PlaymodesStudio/Sonograf/PHOTOS/board_hole.jpg

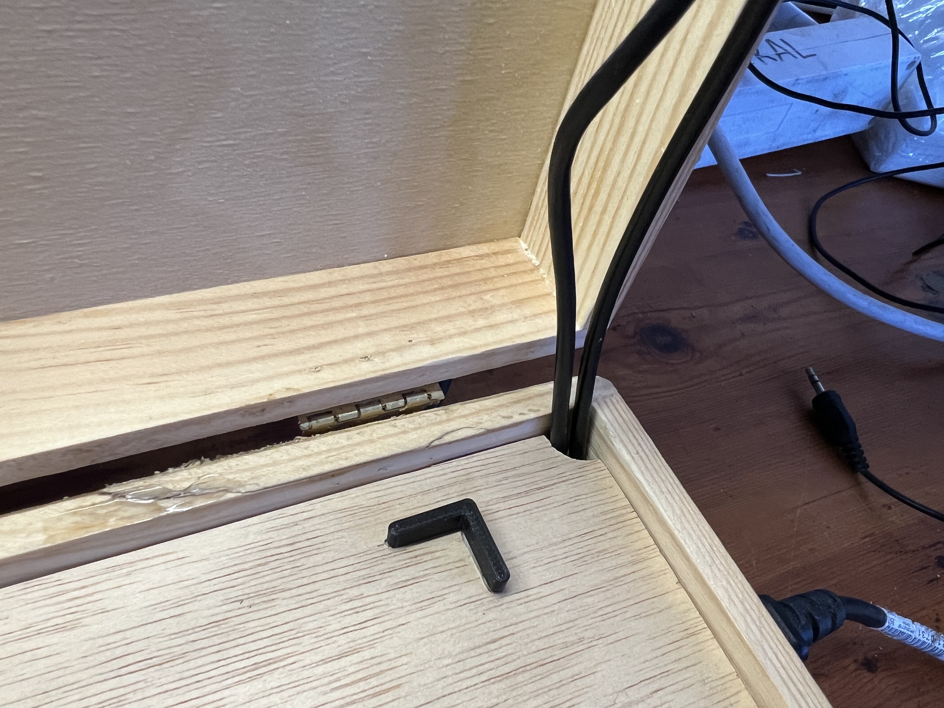
PHOTOS/board_hole.jpg
