PlaymodesStudio/Sonograf/PHOTOS/camera_base.jpg

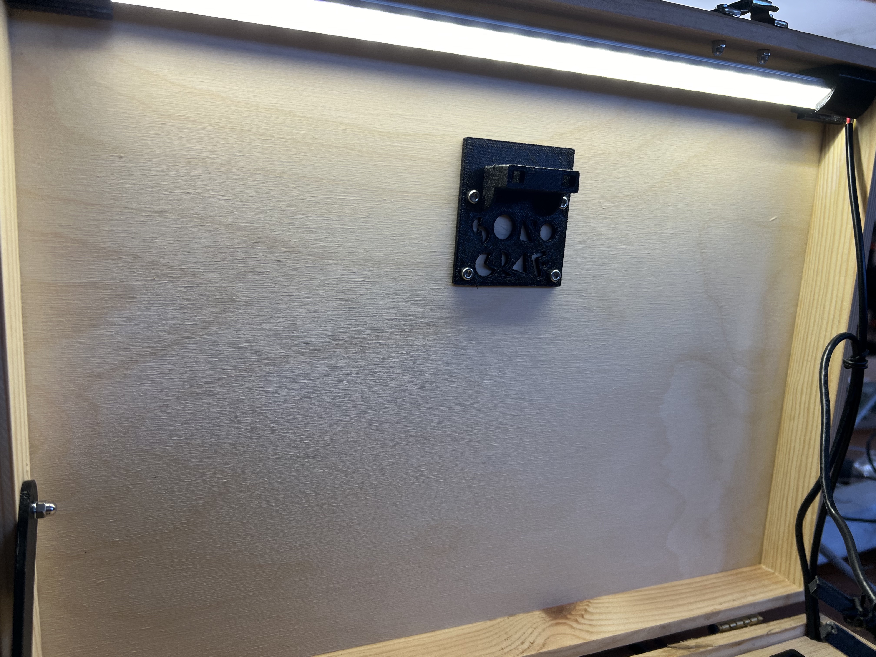
PHOTOS/camera_base.jpg
