PlaymodesStudio/Sonograf/PHOTOS/camera_match.jpg

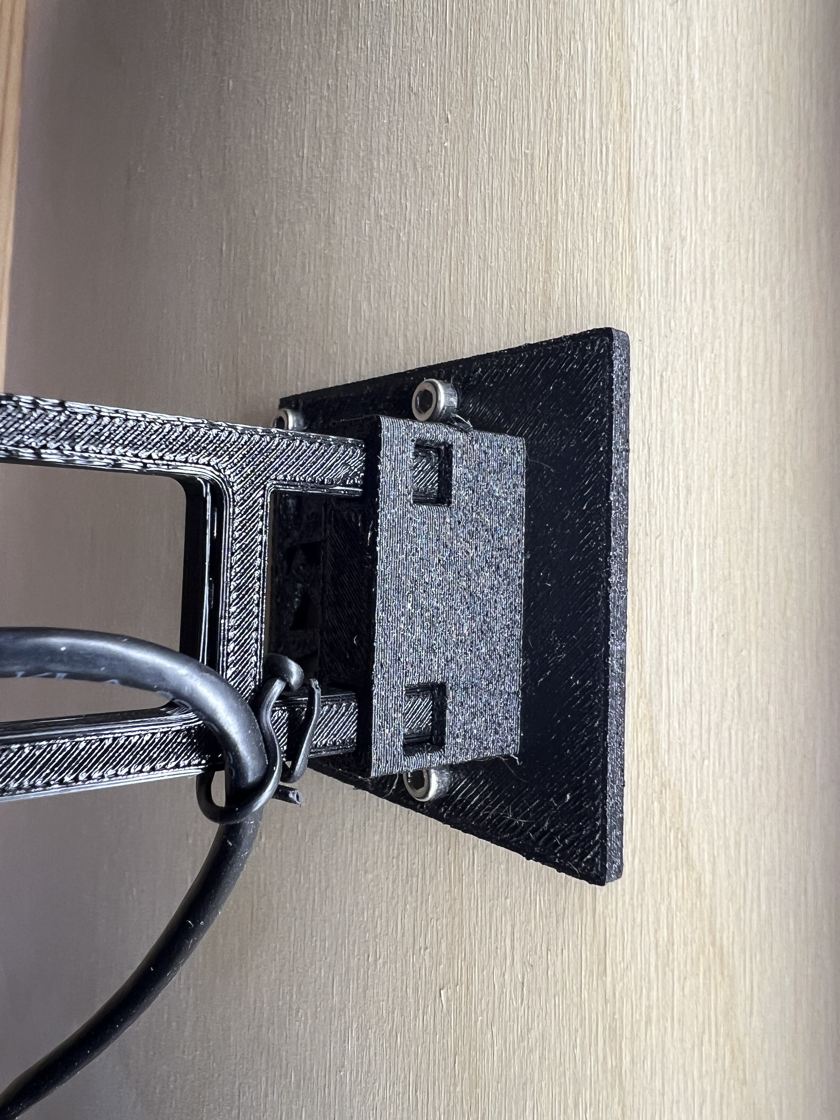
PHOTOS/camera_match.jpg
