PlaymodesStudio/Sonograf/PHOTOS/camera_support.jpg

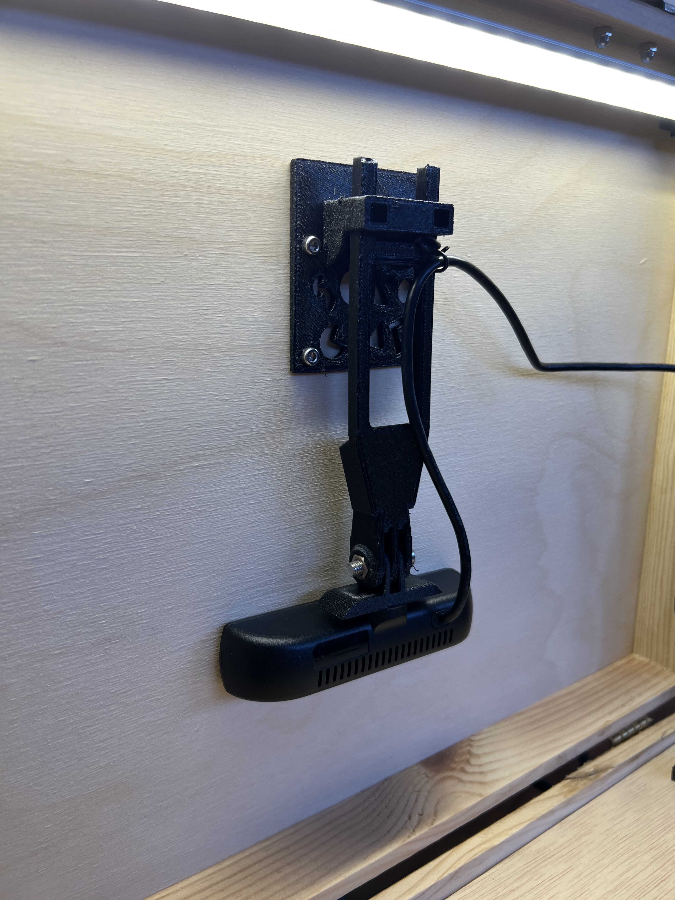
PHOTOS/camera_support.jpg
