PlaymodesStudio/Sonograf/PHOTOS/case_cover.jpg

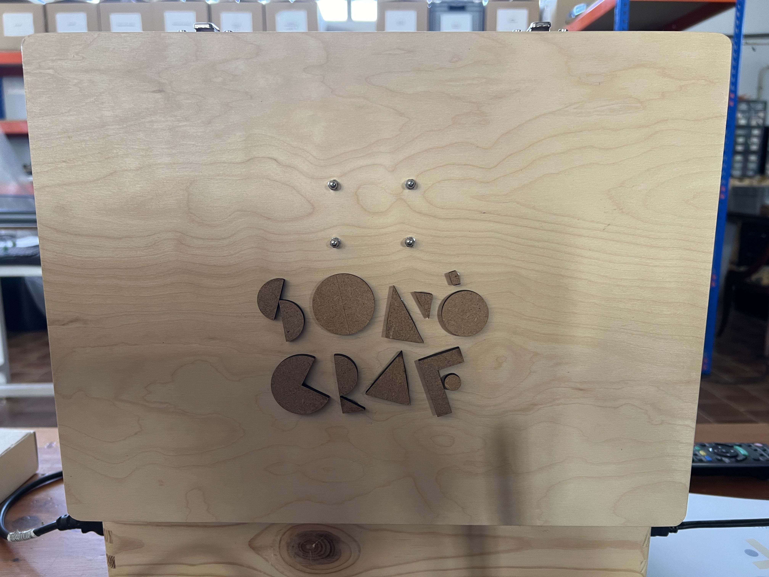
PHOTOS/case_cover.jpg
