PlaymodesStudio/Sonograf/PHOTOS/diagram.png

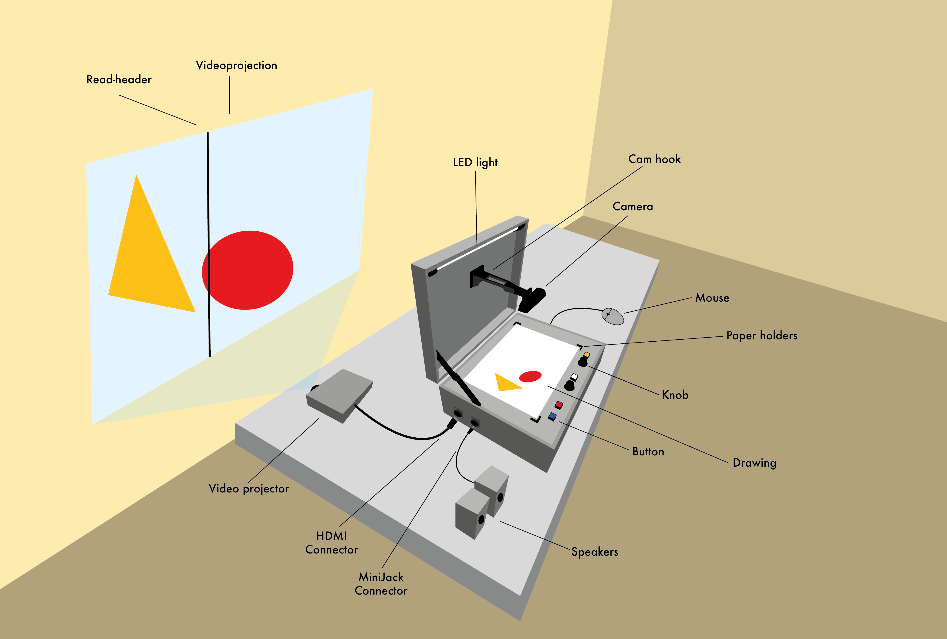
PHOTOS/diagram.png
