PlaymodesStudio/Sonograf/PHOTOS/HDMI.jpg

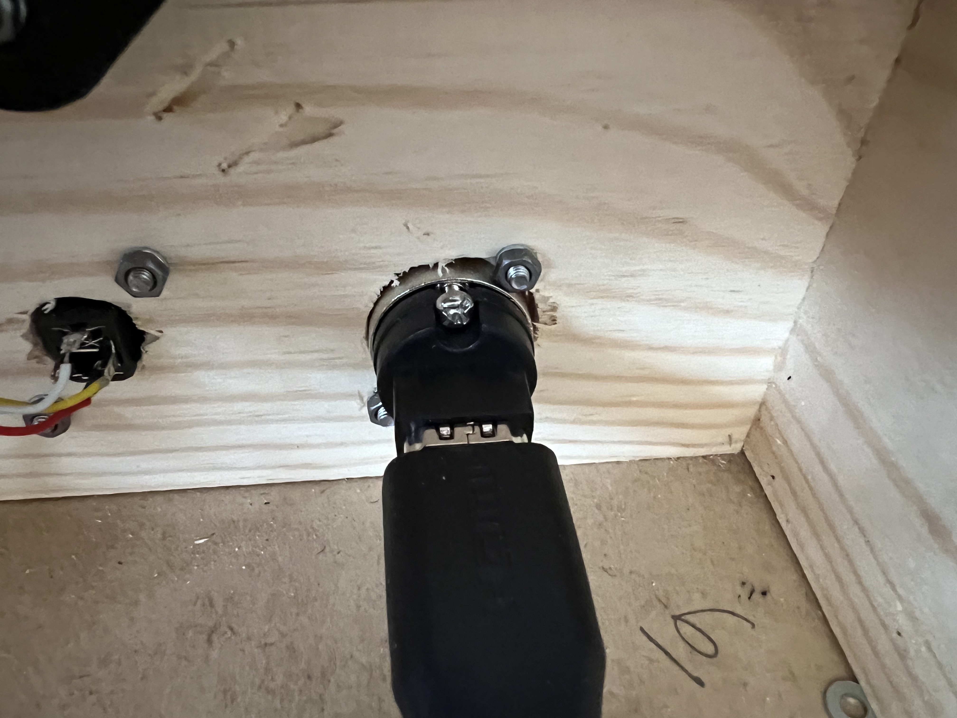
PHOTOS/HDMI.jpg
