PlaymodesStudio/Sonograf/PHOTOS/inner_view.jpg

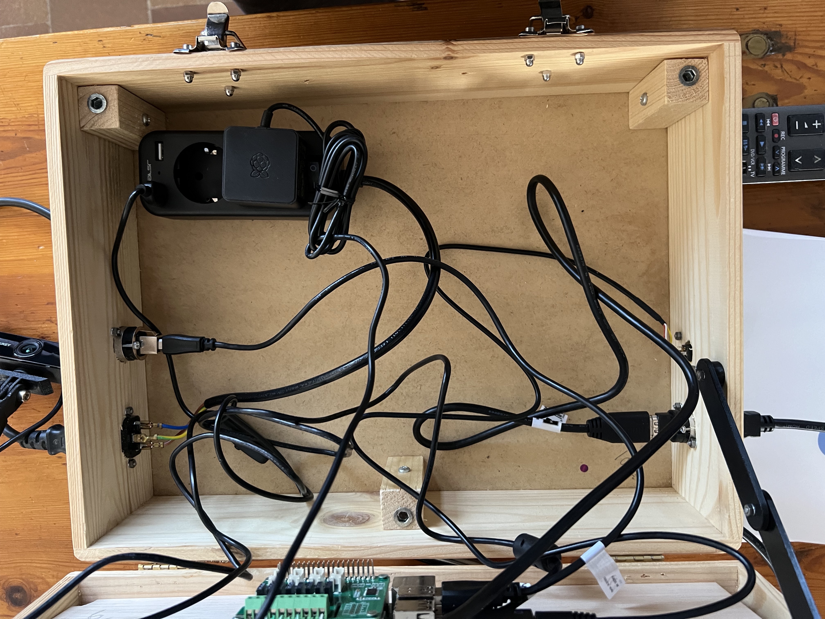
PHOTOS/inner_view.jpg
