PlaymodesStudio/Sonograf/PHOTOS/latch1.jpg

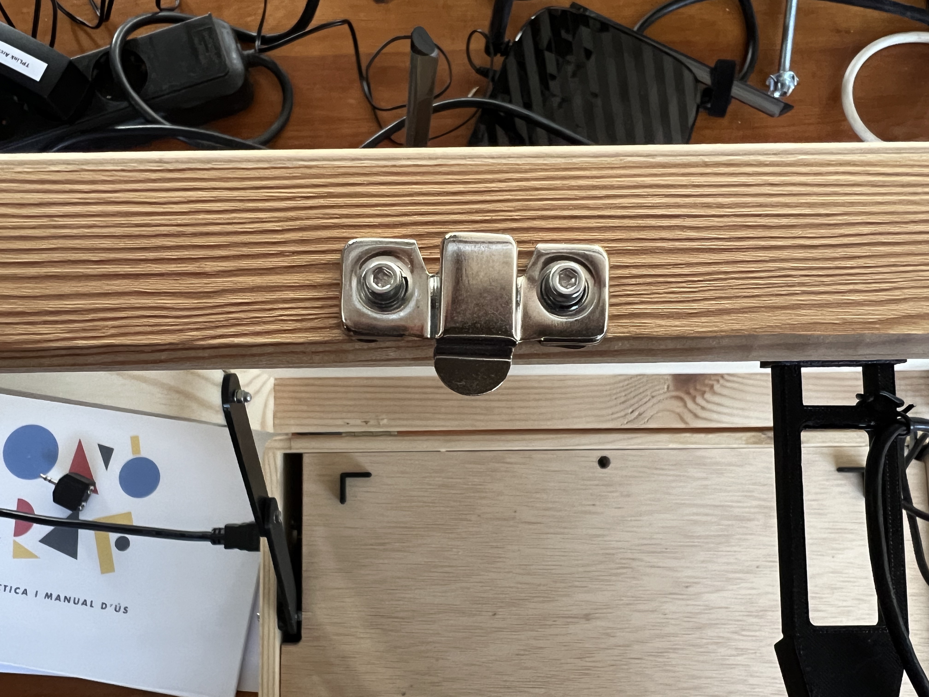
PHOTOS/latch1.jpg
