PlaymodesStudio/Sonograf/PHOTOS/RPI_adc.jpg

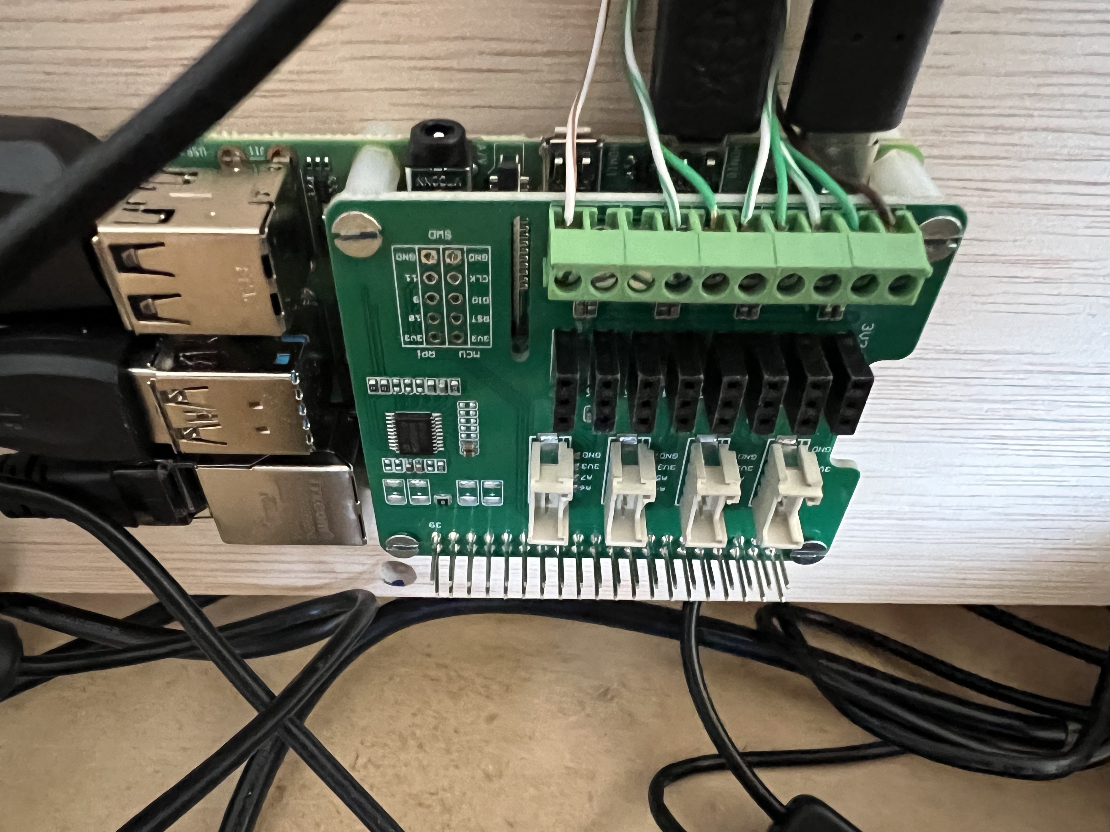
PHOTOS/RPI_adc.jpg
