PlaymodesStudio/Sonograf/PHOTOS/rpi_connections.jpg

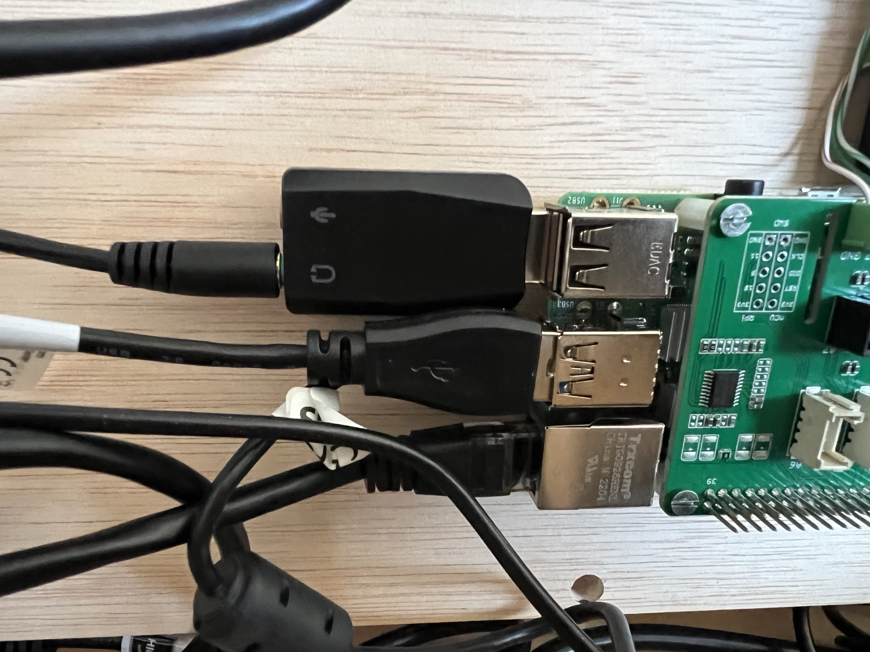
PHOTOS/rpi_connections.jpg
