PlaymodesStudio/Sonograf/PHOTOS/button_wiring.jpg

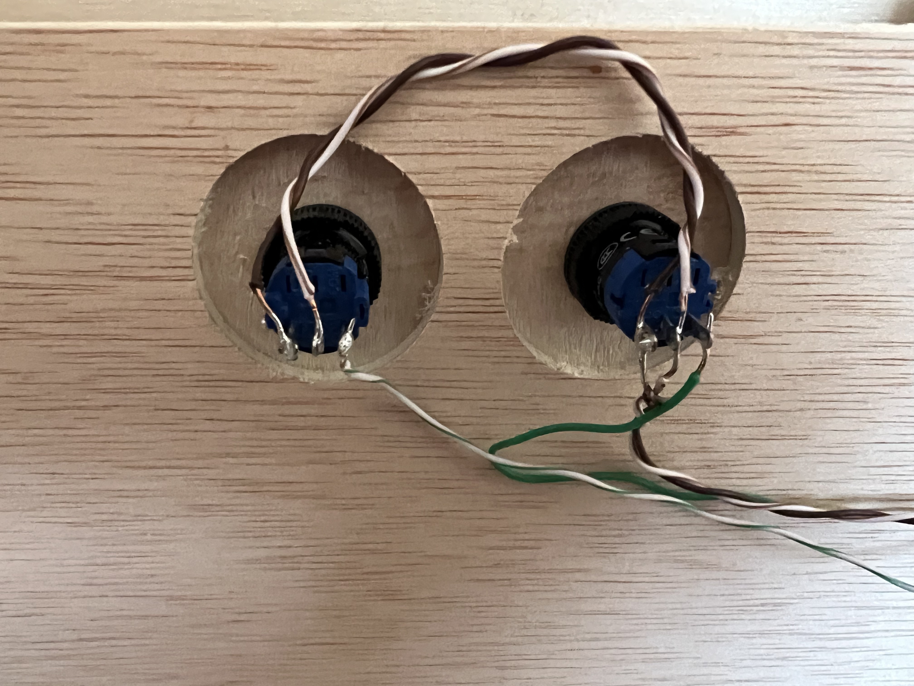
PHOTOS/button_wiring.jpg
