PlaymodesStudio/Sonograf/PHOTOS/final_setup.jpg

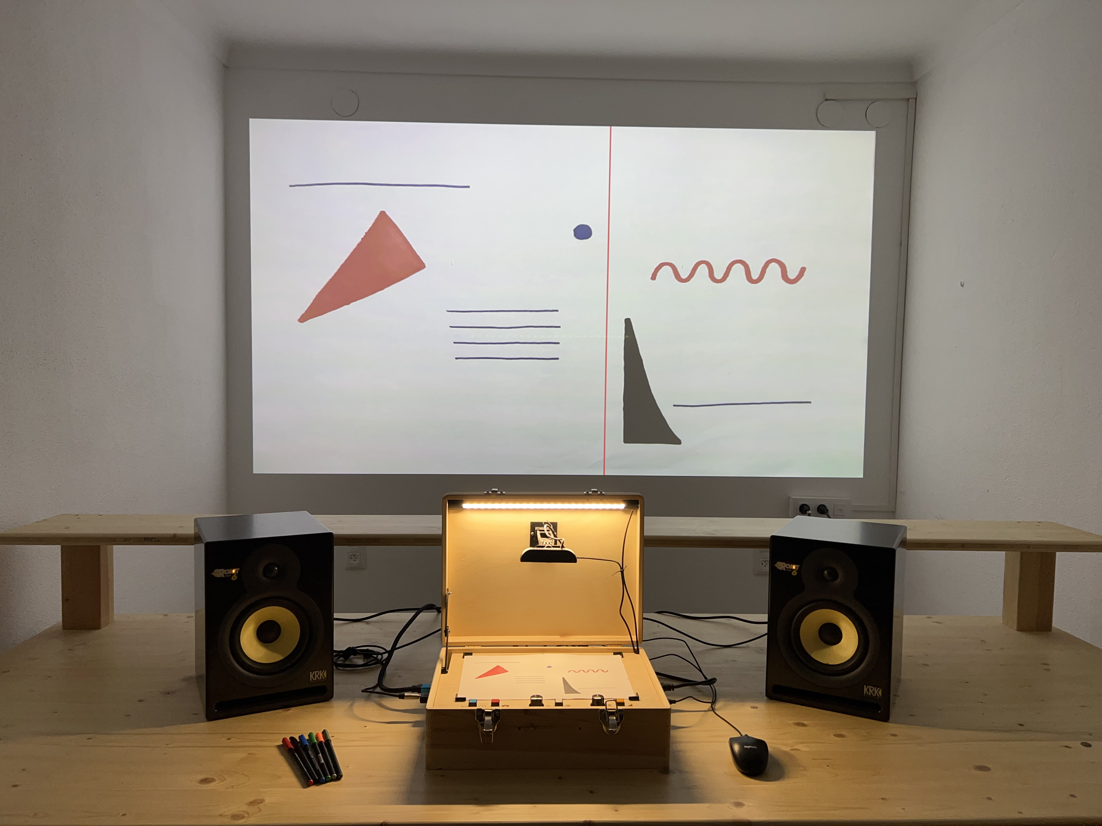
PHOTOS/final_setup.jpg
