PlaymodesStudio/Sonograf/PHOTOS/IEC_wiring.jpg

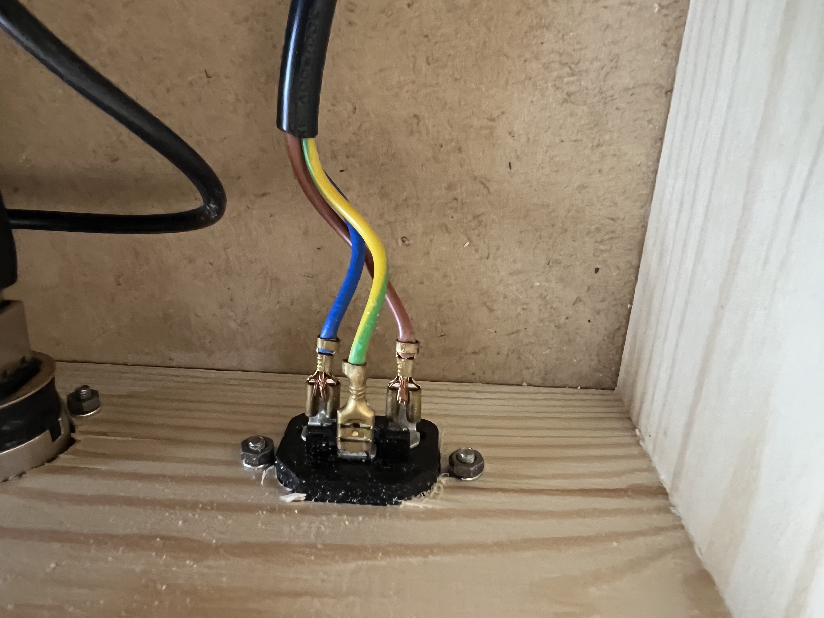
PHOTOS/IEC_wiring.jpg
