PlaymodesStudio/Sonograf/PHOTOS/knob_wiring.jpg

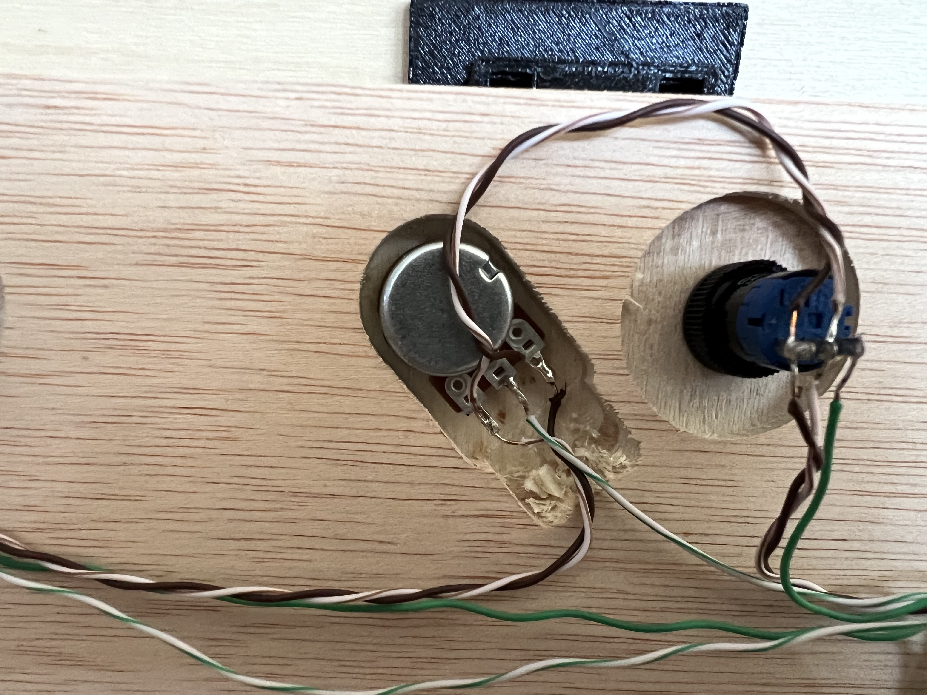
PHOTOS/knob_wiring.jpg
