PlaymodesStudio/Sonograf/WIRING/Sonograf_controls_connections.png

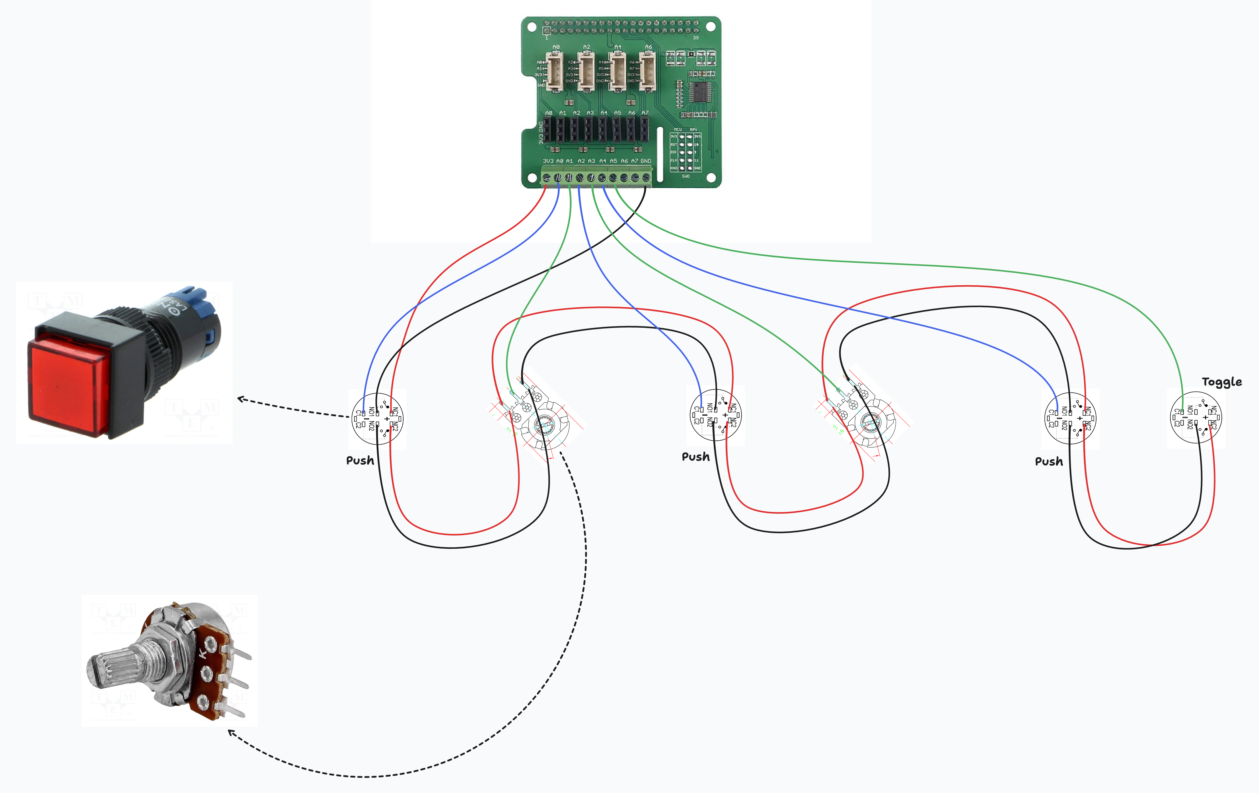
WIRING/Sonograf_controls_connections.png
